kisst/stackable-disk-bay/scad/caddy_tray.scad

// Caddy tray (print flat on its floor). Pins, fingers, spring locks, tabs for the bezel.
include <params.scad>
use <caddy.scad>
caddy_tray();
