kisst/stackable-disk-bay/scad/rear.scad

// Bay rear panel (print one per bay, flat). SATA cutout at the bottom, tongues
// along the side edges for the wall grooves.
include <params.scad>
use <bay.scad>
rear();
