kisst/stackable-disk-bay/scad/wall.scad

// Bay wall (print two per bay, flat, bumps up). Same part is left and right.
include <params.scad>
use <bay.scad>
wall();
